pepetech/usb-can/cad/hv0a/1.png

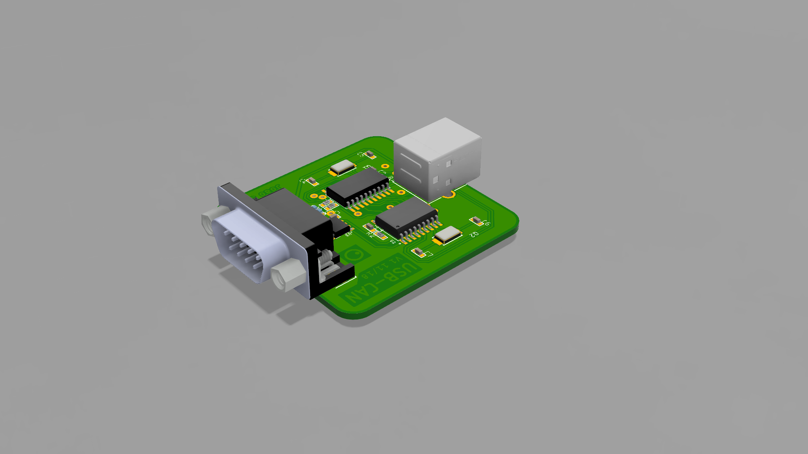
cad/hv0a/1.png
