pepetech/usb-can/cad/hv0a/2.png

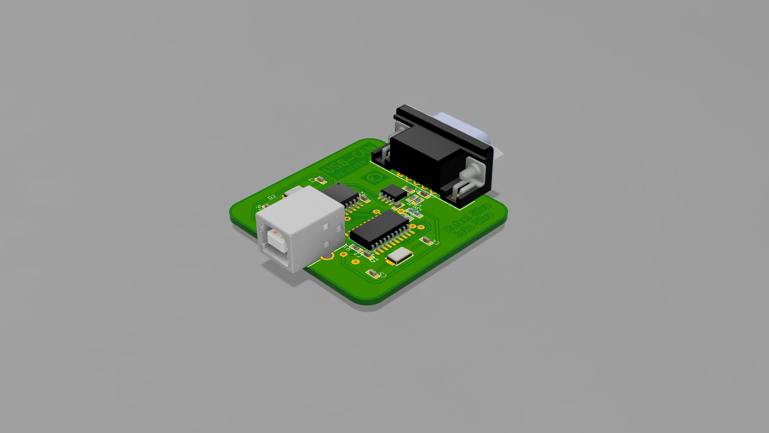
cad/hv0a/2.png
