pepetech/usb-can/cad/hv0a/3.png

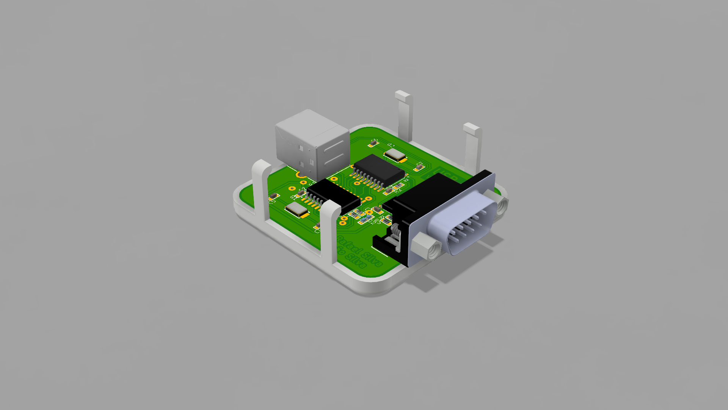
cad/hv0a/3.png
