pepetech/usb-can/cad/hv0a/4.png

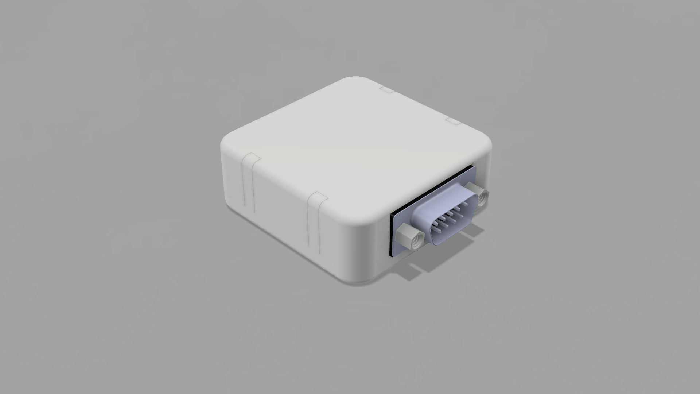
cad/hv0a/4.png
