pepetech/usb-can/cad/hv0a/5.png

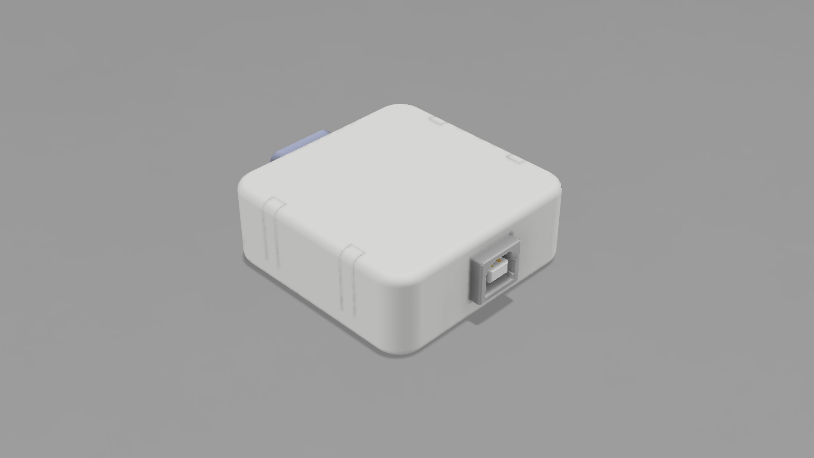
cad/hv0a/5.png
