pepetech/usb-can/cad/hv0a/6.png

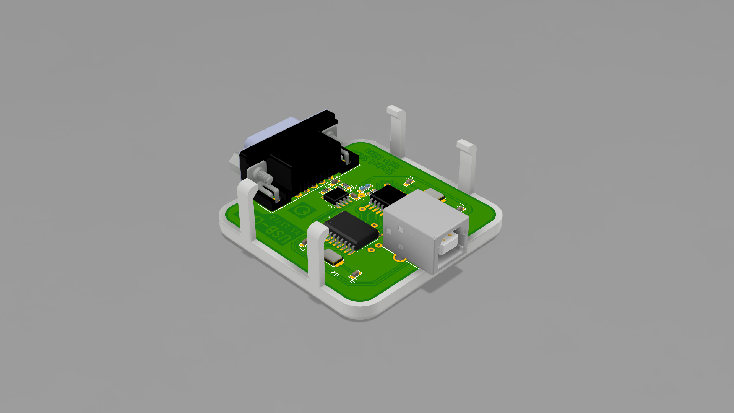
cad/hv0a/6.png
