pepetech/usb-can/cad/hv0a/asm_2018-Nov-21_03-19-31AM-000_CustomizedView13928471128.png

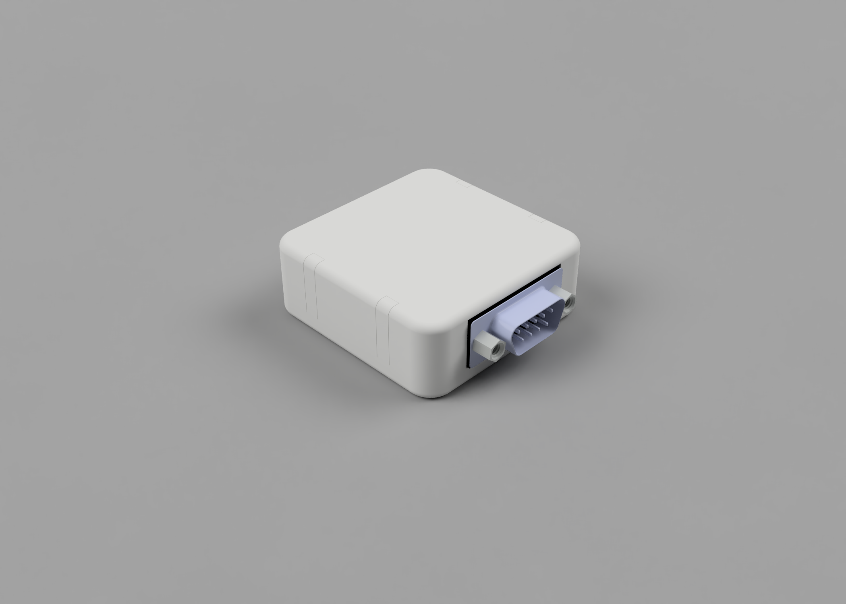
cad/hv0a/asm_2018-Nov-21_03-19-31AM-000_CustomizedView13928471128.png
