pepetech/usb-can/hardware/hv0a/usb-can-bot.png

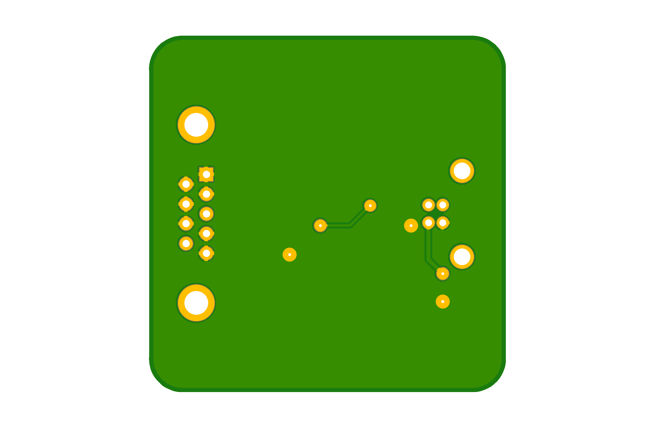
hardware/hv0a/usb-can-bot.png
